ErroujiOussama/Arm-Robot/Simulation/robotics_tool_box_python/arm_robot/readme.jpeg

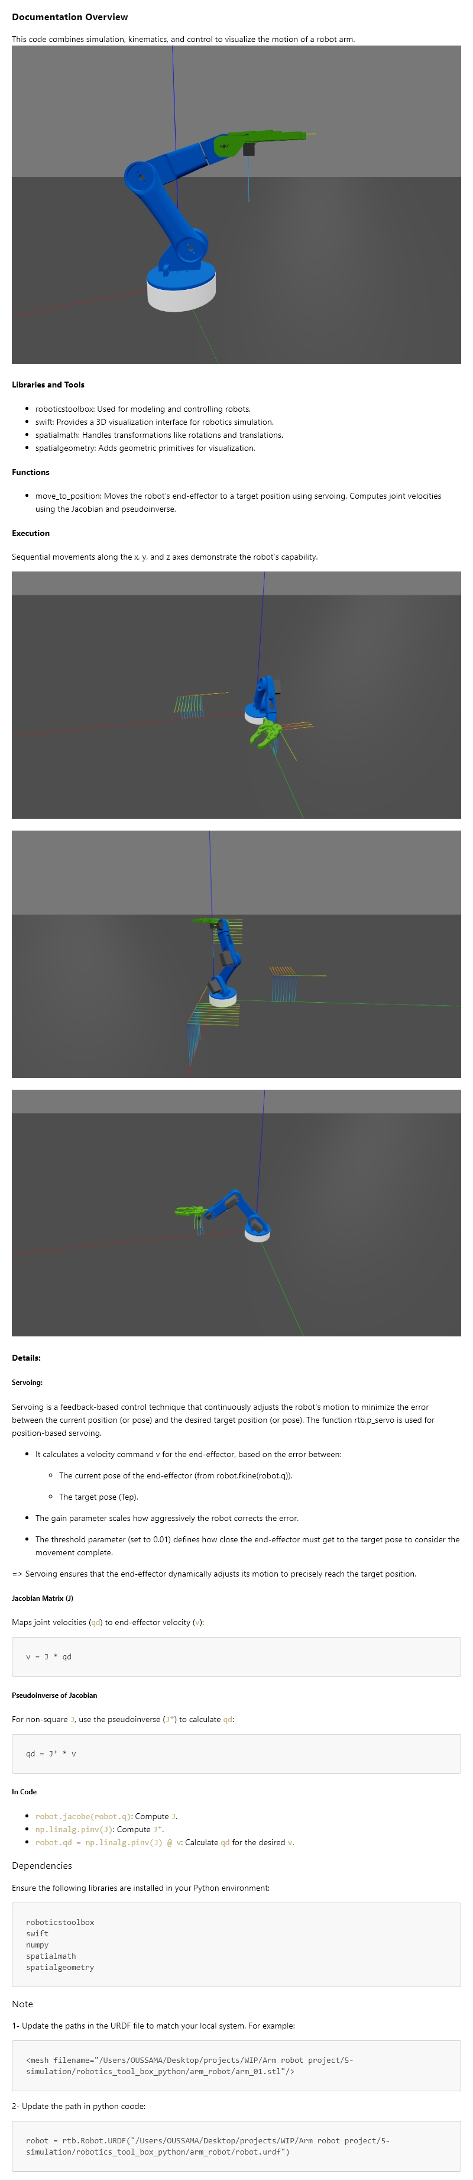
Simulation/robotics_tool_box_python/arm_robot/readme.jpeg
