ErroujiOussama/Arm-Robot/Simulation/Simscape/Arm 03.step

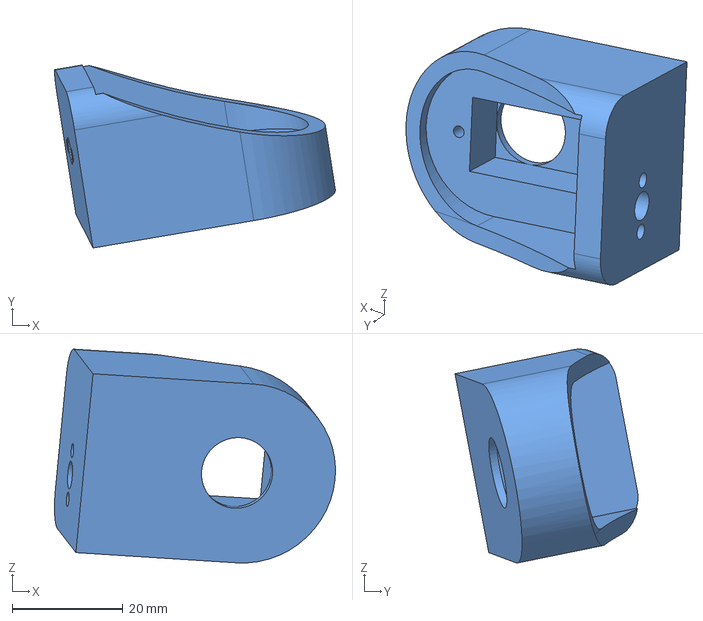
[picture p31: CAD file, 2025-01-12]
Simulation/Simscape/Arm 03.step
50.7 x 33.0 x 38.6 mm
