ErroujiOussama/Arm-Robot/3d Model/3d model/STL/Gripper base.STL

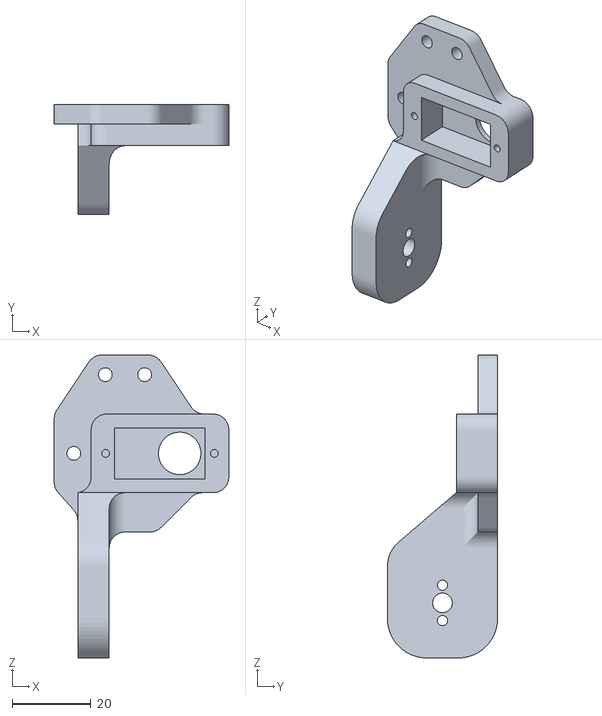
[picture p32: CAD file, 2025-01-12]
3d Model/3d model/STL/Gripper base.STL
44.4 x 28.0 x 77.0
