ErroujiOussama/Arm-Robot/Simulation/pybullet/arm_robot_with_tool/arm_01.stl

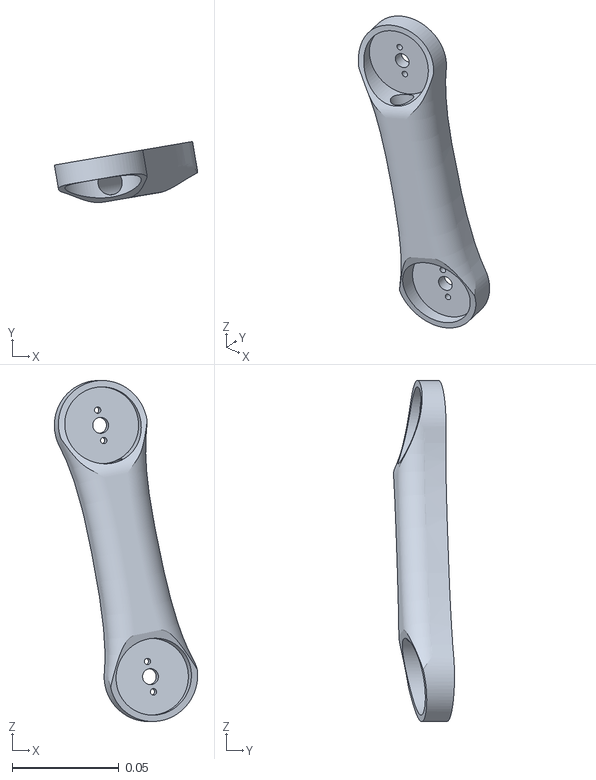
[picture p33: CAD file, 2025-01-12]
Simulation/pybullet/arm_robot_with_tool/arm_01.stl
0.0671 x 0.0286 x 0.16
