ErroujiOussama/Arm-Robot/Simulation/robotics_tool_box_python/arm_robot/meshes/arm_03.stl

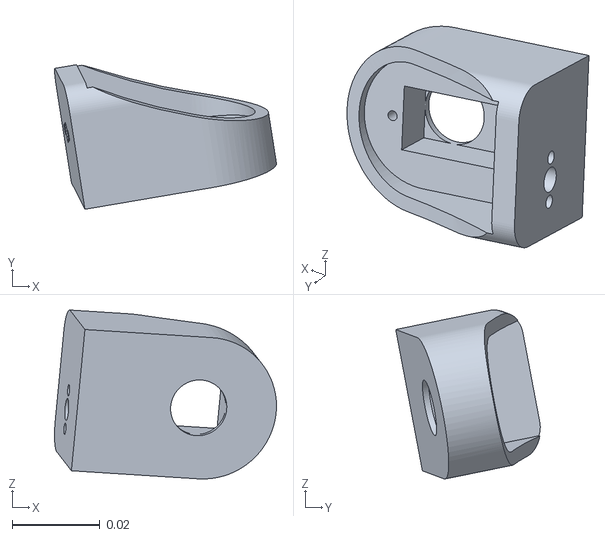
[picture p34: CAD file, 2025-01-12]
Simulation/robotics_tool_box_python/arm_robot/meshes/arm_03.stl
0.0507 x 0.033 x 0.0386
