ErroujiOussama/Arm-Robot/Simulation/Simscape/Gripper Base.step

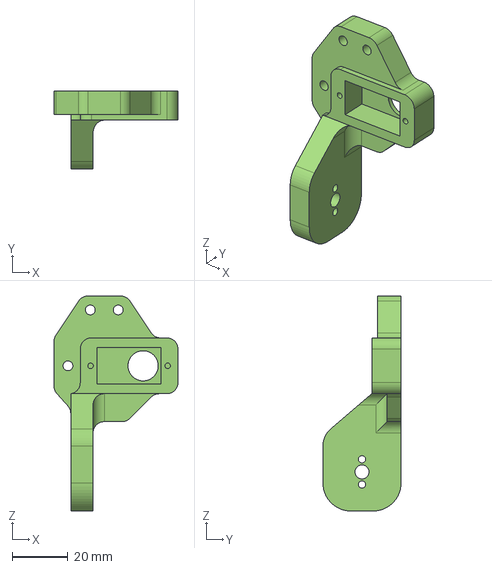
[picture p35: CAD file, 2025-01-12]
Simulation/Simscape/Gripper Base.step
44.4 x 28.0 x 77.0 mm
