ErroujiOussama/Arm-Robot/3d Model/3d model/STL/gear2.STL

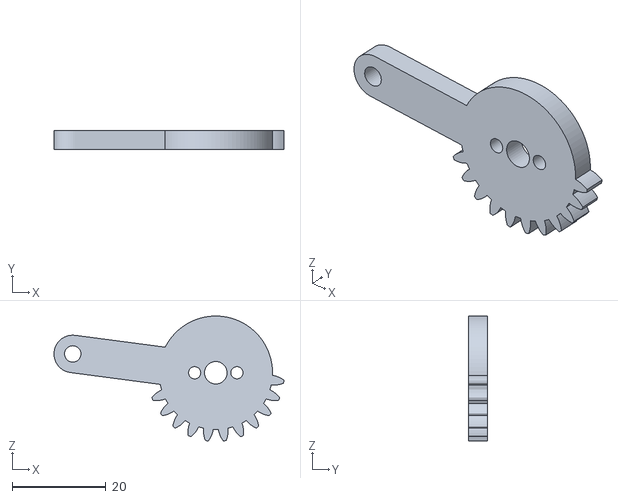
[picture p36: CAD file, 2025-01-12]
3d Model/3d model/STL/gear2.STL
49.0 x 4.00 x 26.6
