ErroujiOussama/Arm-Robot/Simulation/pybullet/arm_robot_with_tool/gripper.stl

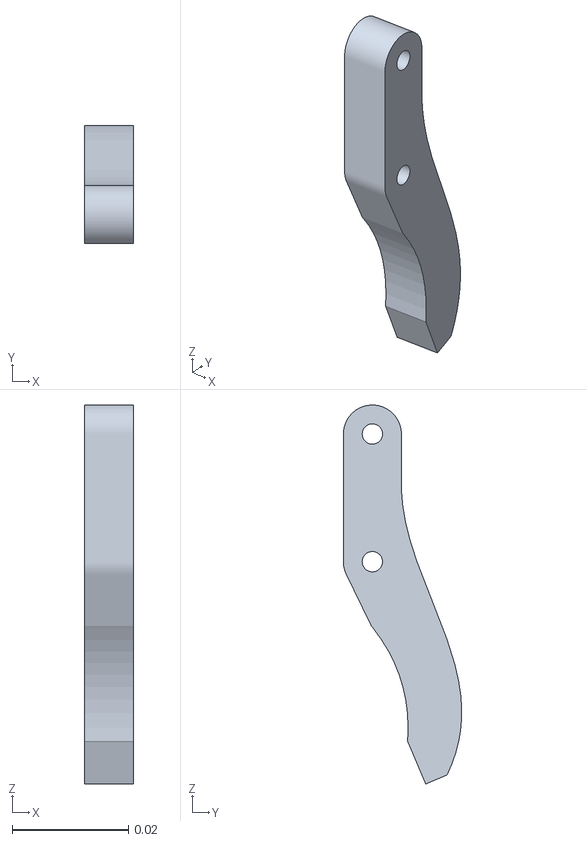
[picture p37: CAD file, 2025-01-12]
Simulation/pybullet/arm_robot_with_tool/gripper.stl
0.0085 x 0.0204 x 0.0653
