ErroujiOussama/Arm-Robot/Simulation/Simscape/Gripper.step

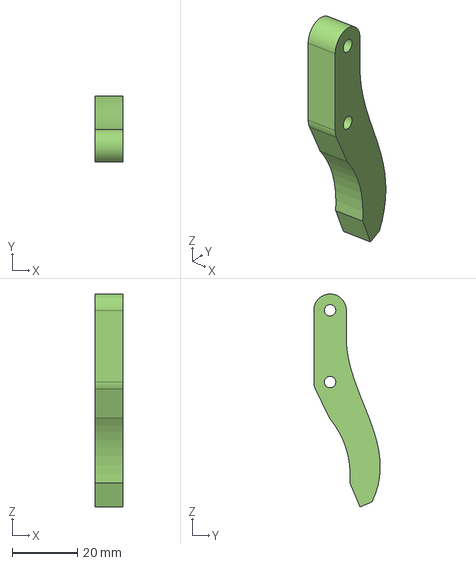
[picture p38: CAD file, 2025-01-12]
Simulation/Simscape/Gripper.step
8.50 x 20.4 x 65.3 mm
