ErroujiOussama/Arm-Robot/Simulation/pybullet/arm_robot_with_tool/base.stl

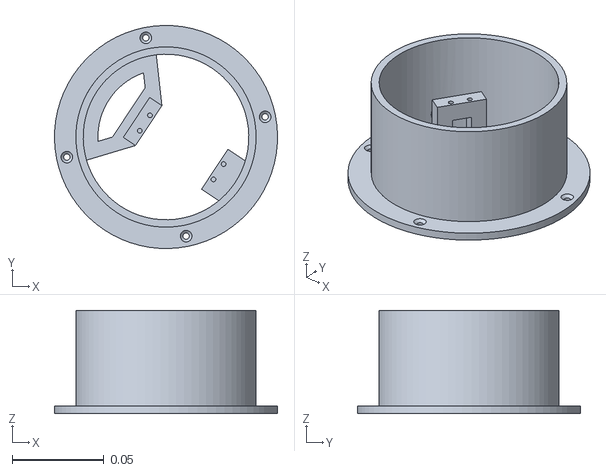
[picture p39: CAD file, 2025-01-12]
Simulation/pybullet/arm_robot_with_tool/base.stl
0.121 x 0.121 x 0.056
