ErroujiOussama/Arm-Robot/Simulation/robotics_tool_box_python/arm_robot/meshes/servo_motor_mg996r_2.stl

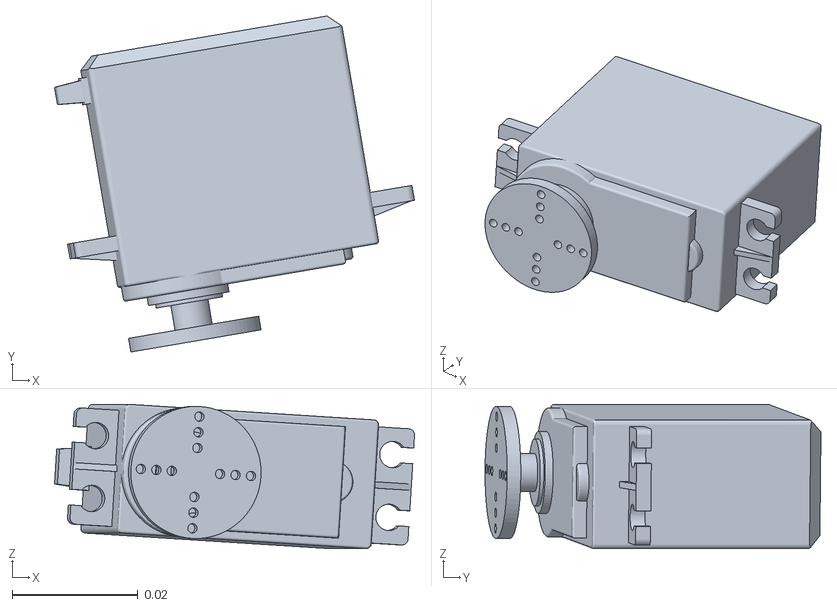
[picture p40: CAD file, 2025-01-12]
Simulation/robotics_tool_box_python/arm_robot/meshes/servo_motor_mg996r_2.stl
0.0572 x 0.0534 x 0.0229
