ErroujiOussama/Arm-Robot/Simulation/Simscape/Arm 01.step

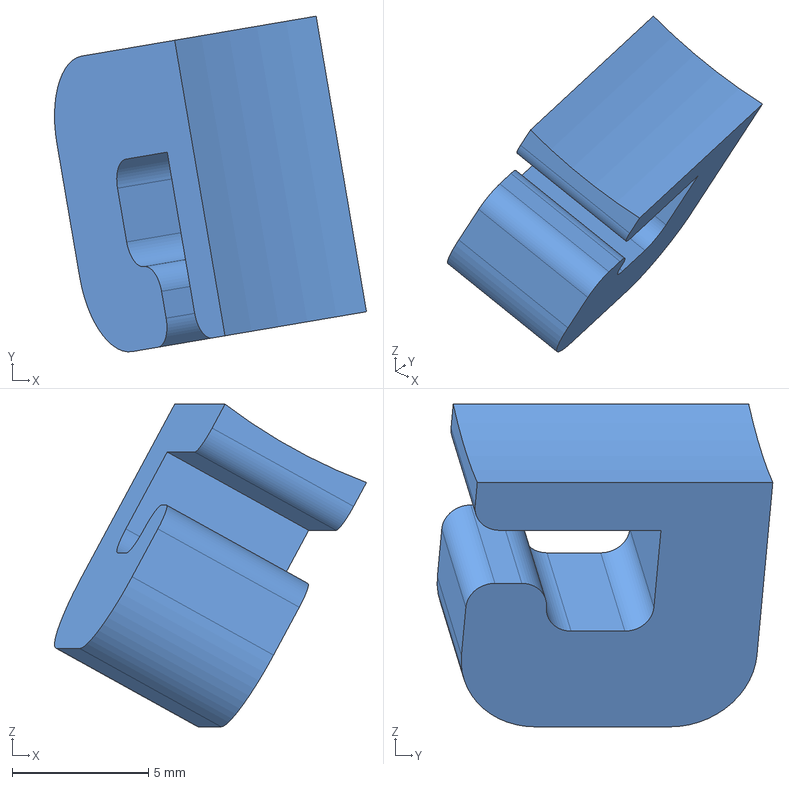
[picture p41: CAD file, 2025-01-12]
Simulation/Simscape/Arm 01.step
11.4 x 12.3 x 11.8 mm
