ErroujiOussama/Arm-Robot/3d Model/3d model/STL/Arm 02 v3.STL

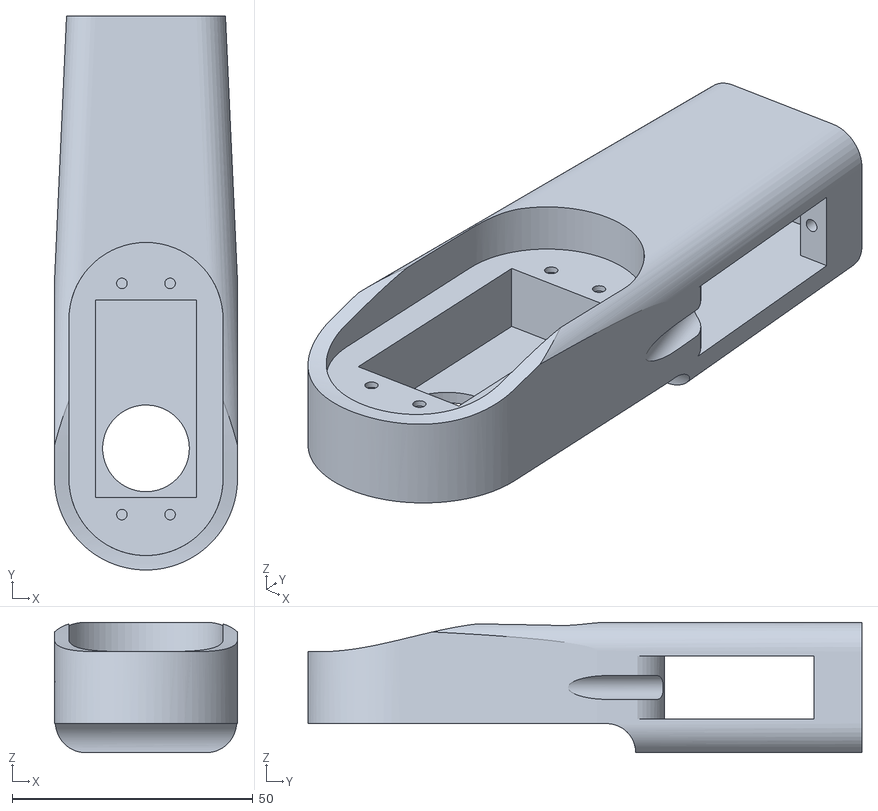
[picture p42: CAD file, 2025-01-12]
3d Model/3d model/STL/Arm 02 v3.STL
38.0 x 115.0 x 27.0
