ErroujiOussama/Arm-Robot/Simulation/robotics_tool_box_python/arm_robot/meshes/gripper_base.stl

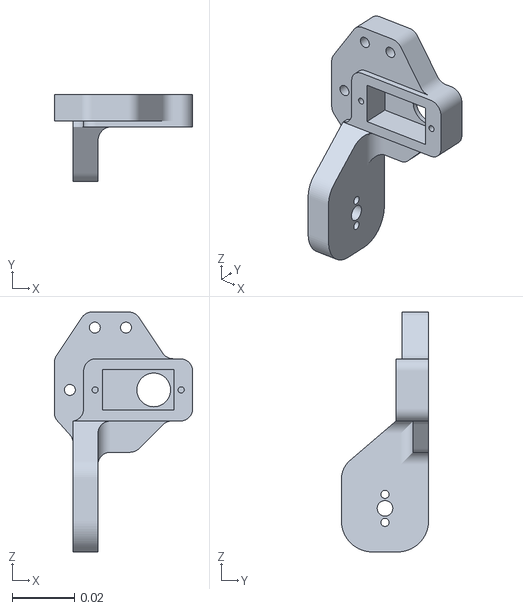
[picture p43: CAD file, 2025-01-12]
Simulation/robotics_tool_box_python/arm_robot/meshes/gripper_base.stl
0.0444 x 0.028 x 0.077
