ErroujiOussama/Arm-Robot/3d Model/3d model/STL/Arm 03.STL

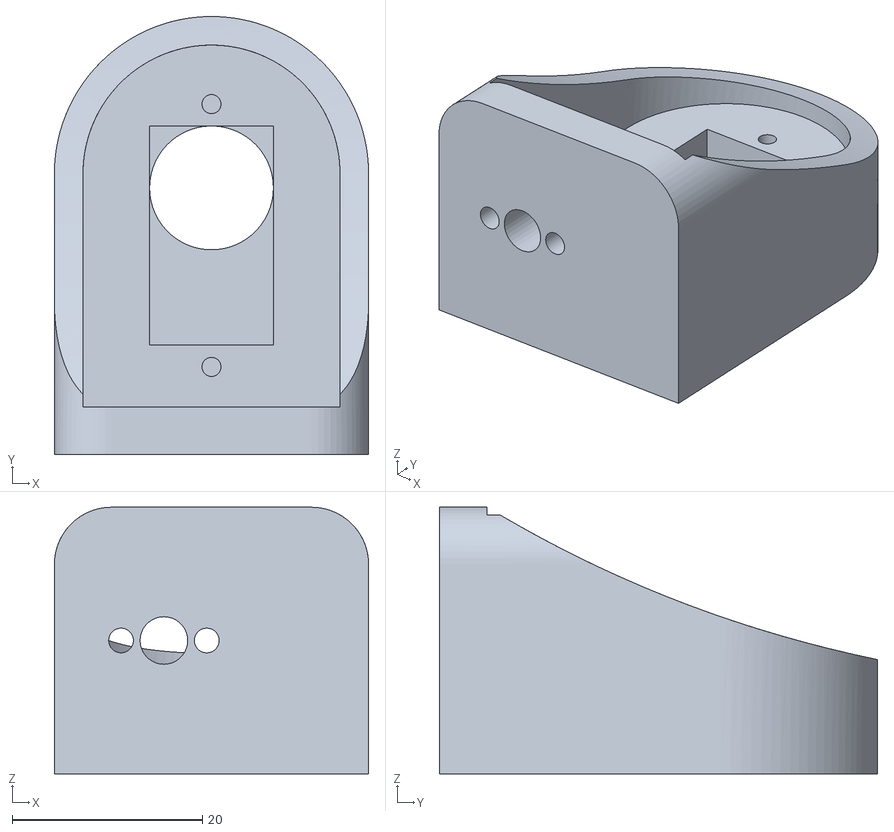
[picture p44: CAD file, 2025-01-12]
3d Model/3d model/STL/Arm 03.STL
33.0 x 46.0 x 28.0
