ErroujiOussama/Arm-Robot/Simulation/pybullet/arm_robot_with_tool/grip_link.stl

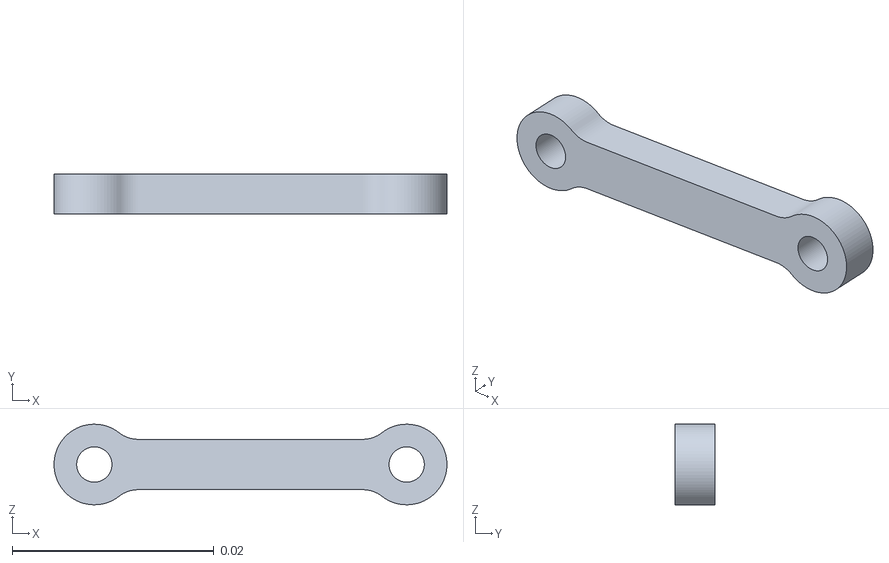
[picture p45: CAD file, 2025-01-12]
Simulation/pybullet/arm_robot_with_tool/grip_link.stl
0.039 x 0.004 x 0.008
