ErroujiOussama/Arm-Robot/Simulation/Simscape/Arm 02 v3.step

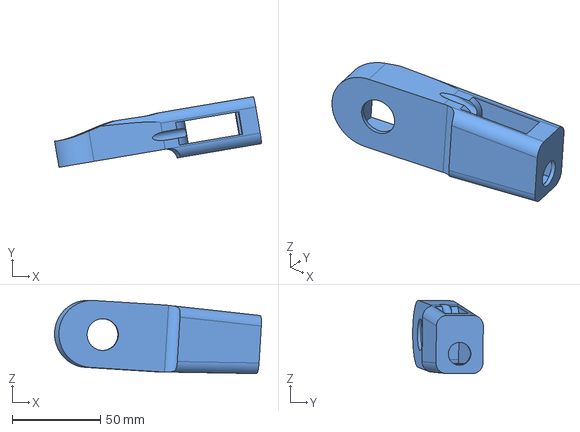
[picture p46: CAD file, 2025-01-12]
Simulation/Simscape/Arm 02 v3.step
117.4 x 40.1 x 41.4 mm
