ErroujiOussama/Arm-Robot/Simulation/Simscape/Servo Motor MG996R.step

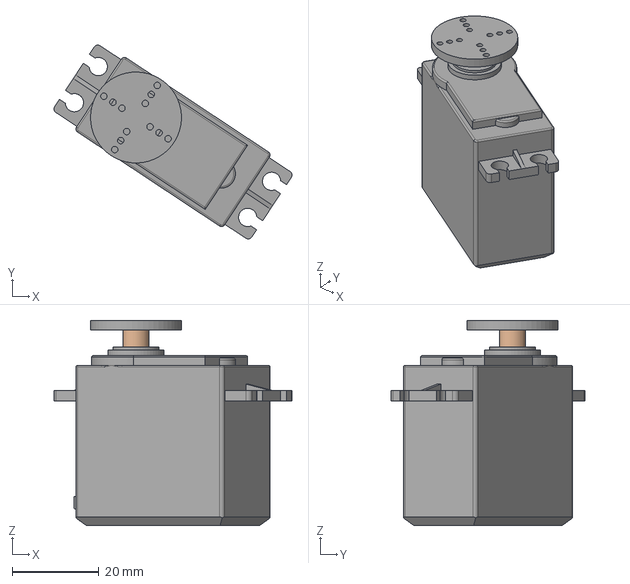
[picture p47: CAD file, 2025-01-12]
Simulation/Simscape/Servo Motor MG996R.step
55.0 x 44.8 x 47.4 mm
