ErroujiOussama/Arm-Robot/Simulation/Simscape/Servo Motor.step

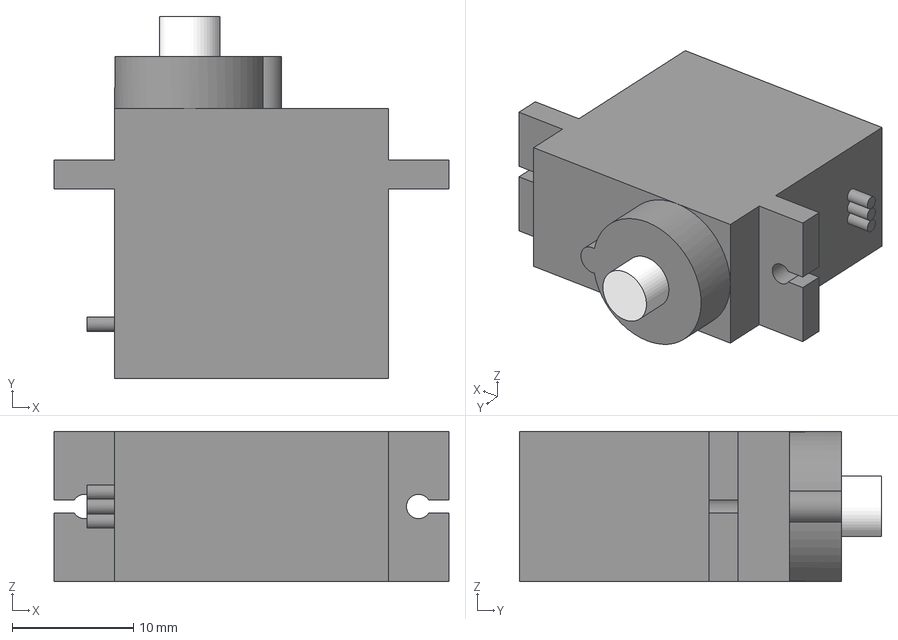
[picture p48: CAD file, 2025-01-12]
Simulation/Simscape/Servo Motor.step
32.6 x 29.9 x 12.4 mm
