ErroujiOussama/Arm-Robot/Simulation/Simscape/Servo Motor Micro  9g_1.step

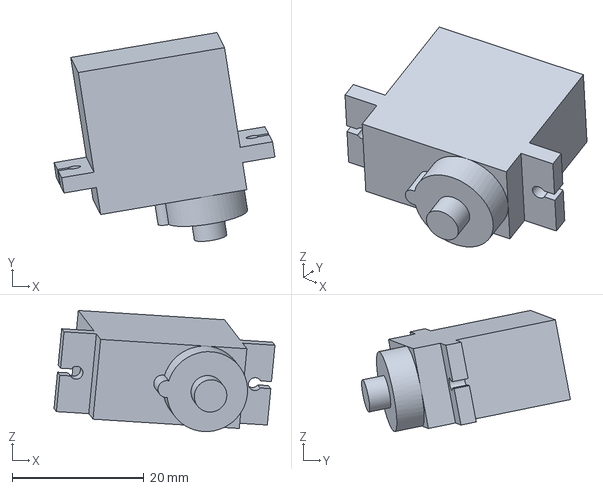
[picture p49: CAD file, 2025-01-12]
Simulation/Simscape/Servo Motor Micro 9g_1.step
33.6 x 31.8 x 18.4 mm
