ErroujiOussama/Arm-Robot/Simulation/Simscape/Servo Motor MG996R_2.step

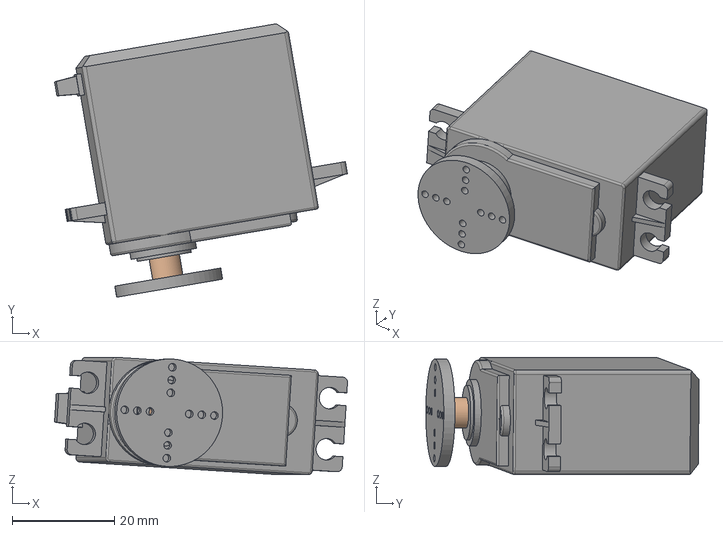
[picture p50: CAD file, 2025-01-12]
Simulation/Simscape/Servo Motor MG996R_2.step
57.2 x 53.4 x 22.9 mm
